avrovulcanxh607/teletext-decoder/PCB Files/decoder.jpg

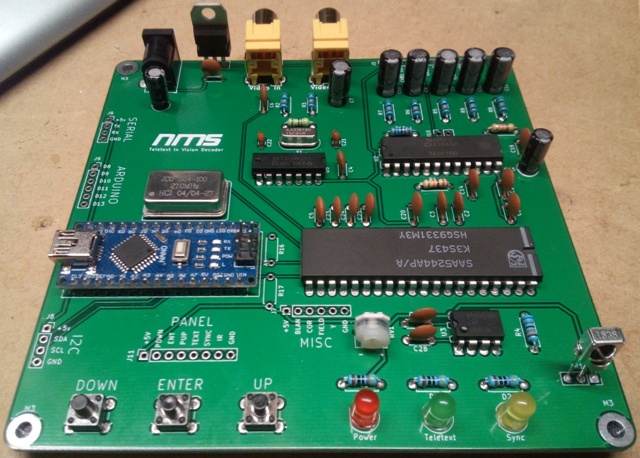
PCB Files/decoder.jpg
