avrovulcanxh607/teletext-decoder/PCB Files/IMG_20200507_191259.jpg

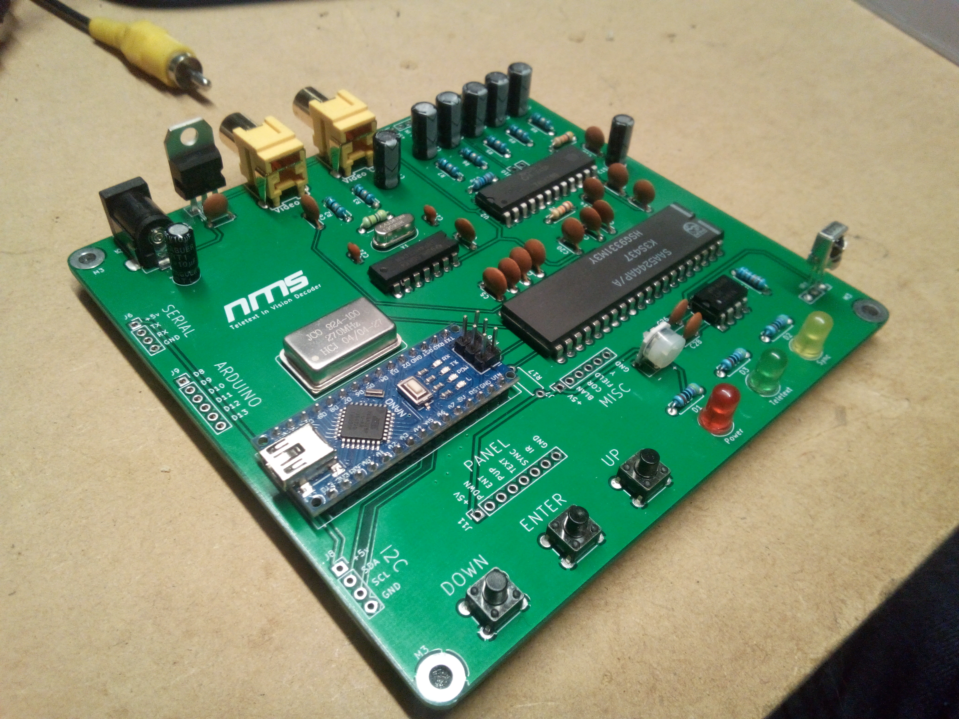
PCB Files/IMG_20200507_191259.jpg
