avrovulcanxh607/teletext-decoder/PCB Files/pcbfordiag.jpg

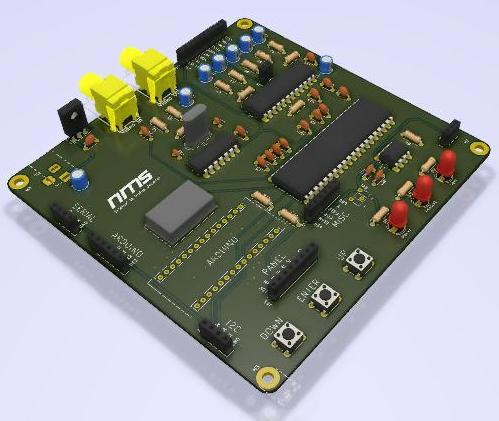
PCB Files/pcbfordiag.jpg
