avrovulcanxh607/teletext-decoder/PCB Files/Teletext In-Vision Decoder.jpg

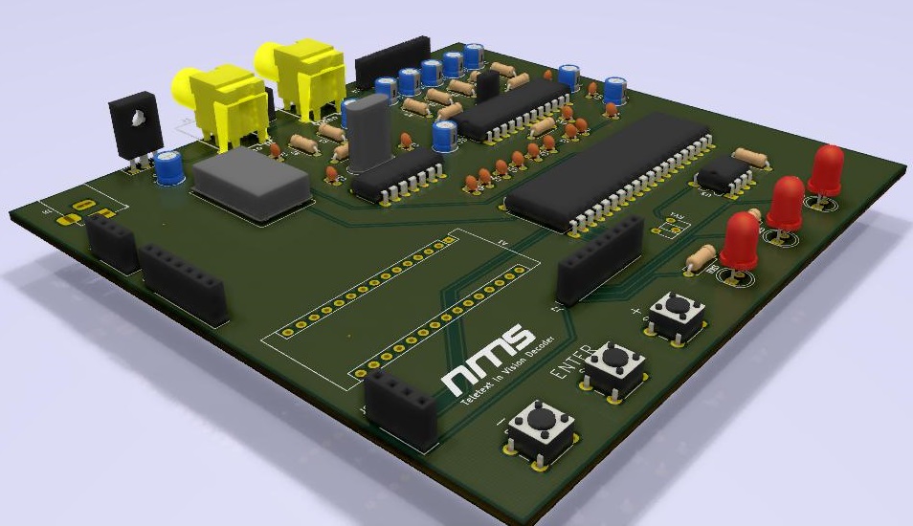
PCB Files/Teletext In-Vision Decoder.jpg
